nofitnessforpurpose/TopSlotBatterySaverBasic/photos/20250913_a.jpg

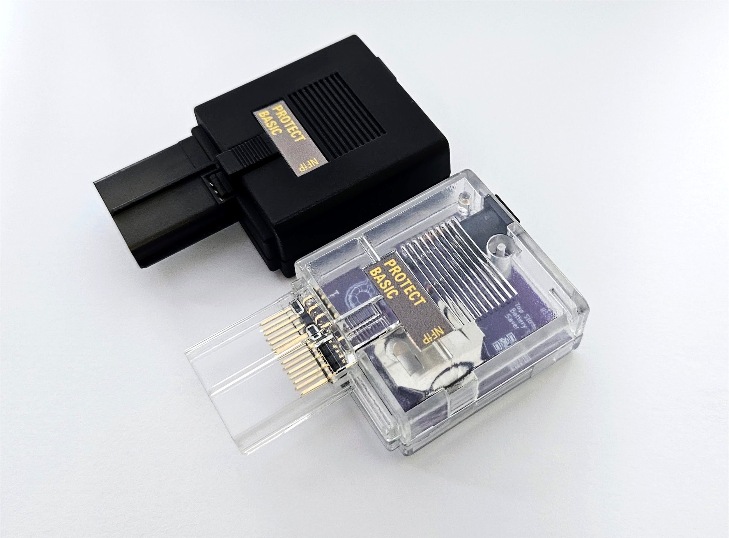
photos/20250913_a.jpg
