nofitnessforpurpose/TopSlotBatterySaverBasic/photos/BATSVE-02.png

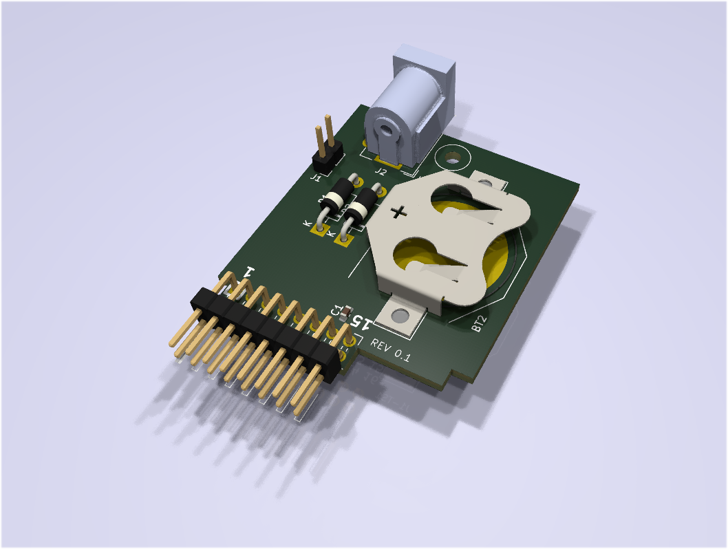
photos/BATSVE-02.png
