nofitnessforpurpose/TopSlotBatterySaverBasic/photos/BATSVE-07.png

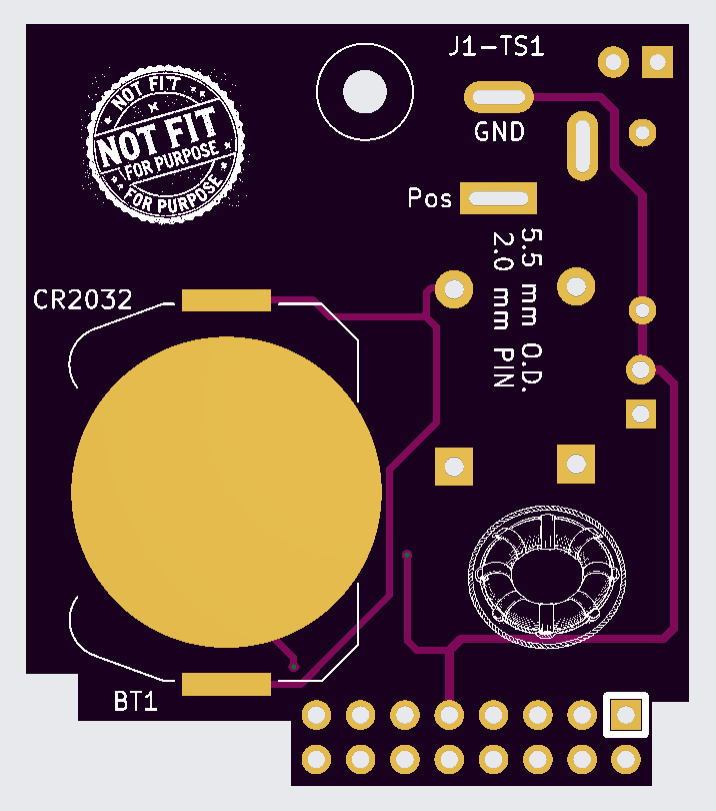
photos/BATSVE-07.png
