nofitnessforpurpose/TopSlotBatterySaverBasic/photos/CPSU-01a.jpg

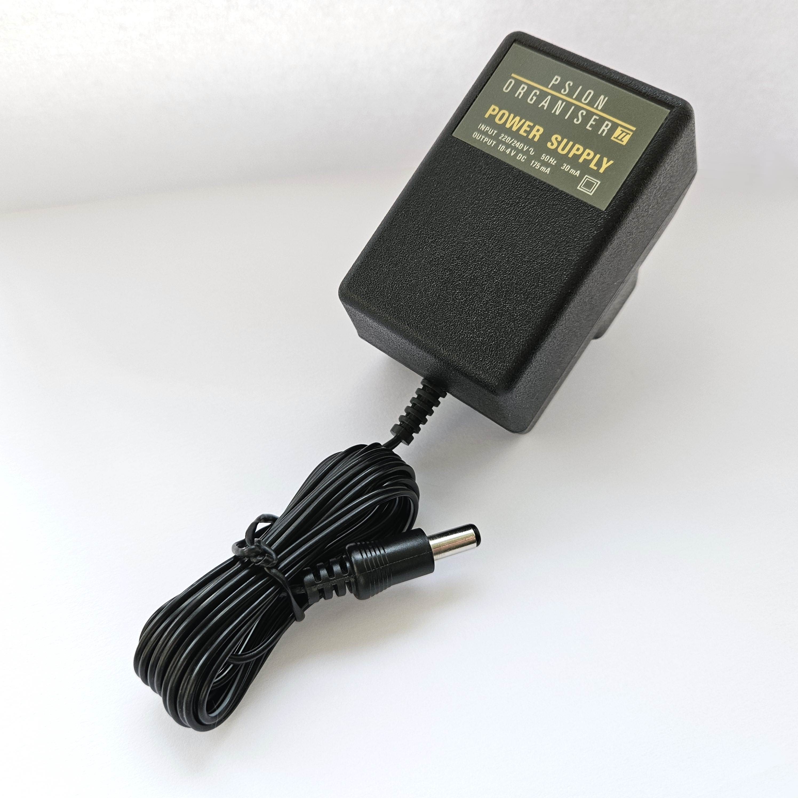
photos/CPSU-01a.jpg
